IiemB/Croaster/boards/common/src/CroasterDisplayAnimation.cpp

#include "CroasterDisplayAnimation.h"

#include <Adafruit_GFX.h>

namespace {
const uint8_t PROGMEM kFireFrames[28][288] = {
    {0,  0,   12,  0,   0,   0,   0,  0,   14,  0,   0,   0,   0,  0,   15,  128, 0,   0,   0,  0,   9,   192, 0,   0,
     0,  0,   24,  224, 0,   0,   0,  0,   24,  56,  0,   0,   0,  0,   56,  28,  0,   0,   0,  0,   48,  14,  0,   0,
     0,  0,   48,  7,   0,   0,   0,  0,   96,  3,   128, 0,   0,  0,   192, 1,   192, 0,   0,  0,   192, 0,   224, 0,
     0,  1,   128, 0,   48,  0,   0,  3,   128, 0,   56,  0,   0,  7,   0,   0,   28,  0,   0,  6,   0,   192, 12,  0,
     0,  12,  0,   224, 6,   0,   0,  24,  0,   240, 7,   0,   0,  56,  0,   248, 3,   0,   0,  112, 0,   220, 1,   128,
     0,  96,  0,   204, 1,   128, 0,  192, 0,   198, 0,   192, 1,  128, 0,   195, 0,   192, 3,  128, 0,   195, 0,   96,
     3,  0,   0,   193, 128, 96,  3,  0,   192, 193, 128, 96,  6,  0,   224, 192, 128, 48,  6,  1,   240, 128, 192, 48,
     12, 1,   185, 128, 192, 48,  12, 3,   31,  0,   192, 48,  12, 3,   6,   0,   192, 48,  12, 3,   0,   0,   192, 48,
     12, 3,   0,   0,   192, 48,  12, 2,   0,   0,   192, 48,  12, 3,   0,   1,   128, 48,  12, 3,   0,   1,   128, 48,
     12, 3,   128, 3,   128, 96,  6,  1,   128, 3,   0,   96,  6,  0,   224, 6,   0,   224, 7,  0,   96,  6,   0,   192,
     3,  0,   0,   0,   0,   192, 3,  128, 0,   0,   1,   128, 1,  192, 0,   0,   3,   0,   0,  224, 0,   0,   7,   0,
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
    display.clearDisplay();
    display.drawBitmap(xPos, yPos, kFireFrames[frame], FRAME_WIDTH, FRAME_HEIGHT, 1);
    display.display();
    frame = (frame + 1) % FRAME_COUNT;
    delay(FRAME_DELAY);
}

void CroasterDisplayAnimation::reset() {
    frame = 0;
}
