IiemB/Croaster/croaster/src/CroasterCommandHandler.cpp

#include "CroasterCommandHandler.h"

#include <ArduinoJson.h>

#include "CroasterConstants.h"
#include "CroasterWiFiManager.h"
#if defined(ESP32)
#    include <WiFi.h>
#elif defined(ESP8266)
#    include <ESP8266WiFi.h>
#endif

CroasterCommandHandler::CroasterCommandHandler(CroasterCore& core, CroasterDisplay* display, int8_t ledPin,
                                               uint8_t ledOnLevel)
    : croaster(core)
    , display(display)
    , ledPin(ledPin)
    , ledOnLevel(ledOnLevel) {}

void CroasterCommandHandler::onCommand(const String& command, CommandFn fn) {
    customCommands[command] = fn;
}

void CroasterCommandHandler::onJsonCommand(const String& key, CommandFn fn) {
    customJsonCommands[key] = fn;
}

void CroasterCommandHandler::begin() {
    if (ledPin >= 0) {
        pinMode(ledPin, OUTPUT);
        digitalWrite(ledPin, (ledOnLevel == HIGH) ? LOW : HIGH);
    }
}

void CroasterCommandHandler::loop() {
    unsigned long now = millis();

    if (blinking && now - lastBlinkTime >= blinkDelay) {
        ledState = !ledState;
        if (ledPin >= 0)
            digitalWrite(ledPin, ledState ? ledOnLevel : ((ledOnLevel == HIGH) ? LOW : HIGH));
        if (display)
            display->blinkIndicator(ledState);
        lastBlinkTime = now;
        blinkCount++;

        if (blinkCount >= blinkTotal) {
            blinking = false;
            if (ledPin >= 0)
                digitalWrite(ledPin, (ledOnLevel == HIGH) ? LOW : HIGH); // turn off when done
            if (display)
                display->blinkIndicator(false); // turn off when done
        }
    }
}

bool CroasterCommandHandler::handle(const String& json, String& responseOut) {
    JsonDocument doc;

    if (deserializeJson(doc, json)) {
        debugln("# Invalid JSON command : " + json);
        return false;
    }

    responseOut = "";

    if (doc["command"].is<String>()) {
        JsonObject json = doc.as<JsonObject>();

        handleBasicCommand(json, responseOut);

        return true;
    }

    if (doc["command"].is<JsonObject>()) {
        JsonObject obj = doc["command"];

        handleJsonCommand(obj, responseOut);

        return true;
    }

    return false;
}

void CroasterCommandHandler::handleBasicCommand(const JsonObject& json, String& responseOut) {
    if (!json["command"].is<String>())
        return;

    String command = json["command"].as<String>();

    if (command == "getArtisanData") {
        int id = json["id"].as<int>();

        responseOut = croaster.getJsonData(id);
    } else if (command == "restartesp") {
        ESP.restart();
    } else if (command == "erase") {
        CroasterWiFiManager::erase();
    } else if (command == "dummyToggle") {
        croaster.toggleDummyData();
    } else if (command == "rotateScreen") {
        if (display)
            display->rotateScreen();
    } else if (command == "blink") {
        blinkBuiltinLED();
    } else if (command == "displayToggle") {
        if (display)
            display->displayToggle();
    } else if (command == "getDeviceInfo") {
        bool darkMode = (display != nullptr) ? display->isDarkMode() : true;
        int brightness = (display != nullptr) ? display->getBrightness() : 100;
        responseOut = genResponseCommand(command, croaster.getDeviceInfo(darkMode, brightness));
    } else if (command == "getExtra") {
        responseOut = genResponseCommand(command, getExtraData());
    } else {
        // Custom implementation-defined command (registered via onCommand()).
        auto it = customCommands.find(command);
        if (it != customCommands.end()) {
            String resp = it->second(json);
            if (!resp.isEmpty())
                responseOut = resp;
        }
    }
}

void CroasterCommandHandler::handleJsonCommand(const JsonObject& json, String& responseOut) {
    if (json["tempUnit"].is<String>()) {
        String tempUnit = json["tempUnit"].as<String>();

        croaster.changeTemperatureUnit(tempUnit);
    }

    if (json["interval"].is<int>()) {
        int interval = json["interval"].as<int>();

        if (interval >= 1)
            croaster.changeIntervalSendData(interval);
    }

    if (json["correctionBt"].is<double>()) {
        double correctionBt = json["correctionBt"].as<double>();

        croaster.changeCorrectionBt(correctionBt);
    }

    if (json["correctionEt"].is<double>()) {
        double correctionEt = json["correctionEt"].as<double>();

        croaster.changeCorrectionEt(correctionEt);
    }

    if (json["wifiConnect"].is<JsonObject>()) {
        JsonObject obj = json["wifiConnect"];

        if (obj["ssid"].is<String>() && obj["pass"].is<String>()) {
            String ssid = obj["ssid"].as<String>();
            String pass = obj["pass"].as<String>();

            WiFi.begin(ssid.c_str(), pass.c_str());

            debugln("# Connecting to " + ssid);
        }
    }

    // Custom implementation-defined nested JSON commands (registered via onJsonCommand()).
    for (auto& entry : customJsonCommands) {
        if (json[entry.first].is<JsonVariant>()) {
            String resp = entry.second(json);
            if (!resp.isEmpty())
                responseOut = resp;
        }
    }
}

void CroasterCommandHandler::blinkBuiltinLED(uint8_t times, unsigned long blinkDelay) {
    blinkTotal = times * 2; // on/off = 2 toggles per blink
    blinkCount = 0;
    lastBlinkTime = millis();
    blinkDelay = blinkDelay;
    ledState = false;

    blinking = true;
}

String CroasterCommandHandler::genResponseCommand(const String command, const String response) {
    JsonDocument doc;

    JsonDocument responseDoc;

    doc["command"] = command;

    if (!response.isEmpty() && !deserializeJson(responseDoc, response)) {
        doc["response"] = responseDoc;
    }

    String jsonOutput;

    serializeJson(doc, jsonOutput);

    return jsonOutput;
}

String CroasterCommandHandler::genRandomString(int length) {
    const char charset[] = "0123456789"
                           "ABCDEFGHIJKLMNOPQRSTUVWXYZ"
                           "abcdefghijklmnopqrstuvwxyz";

    String result;

    for (int i = 0; i < length; i++) {
        result += charset[random(0, sizeof(charset) - 1)];
    }

    return result;
}

String CroasterCommandHandler::getExtraData() {
    /*
   NOTE
   You can add more fields to the JSON document that will be readed by ICRM app,
   such as historical data or other sensor readings.
   */

    JsonDocument doc;

    doc["string"] = genRandomString(10);
    doc["number"] = random(100, 999);
    doc["boolean"] = random(0, 2) == 1;

    String jsonOutput;

    serializeJson(doc, jsonOutput);

    return jsonOutput;
}
