IiemB/Croaster/boards/common/src/CroasterDisplaySSD1306.cpp

#include "CroasterDisplaySSD1306.h"

#include <CroasterConstants.h>
#include <CroasterDeviceIdentity.h>
#include <Wire.h>

#include "CroasterDisplayAnimation.h"

CroasterDisplaySSD1306::CroasterDisplaySSD1306(CroasterCore& croaster, uint8_t i2cAddr)
    : CroasterDisplay(croaster)
    , display(SCREEN_WIDTH, SCREEN_HEIGHT, &Wire, OLED_RESET)
    , i2cAddress(i2cAddr) {}

void CroasterDisplaySSD1306::begin() {
    hasDisplay = isOledPresent();

    if (!hasDisplay) {
        debugln(F("# No display found"));
        return;
    }

    if (!display.begin(SSD1306_SWITCHCAPVCC, i2cAddress)) {
        debugln(F("# SSD1306 allocation failed"));
        return;
    }

    display.clearDisplay();
    display.setTextColor(SSD1306_WHITE);
    debugln(F("# SSD1306 initialization succeed"));
    splash();

    display.setTextWrap(false);
}

void CroasterDisplaySSD1306::drawHeader() {
    if (!hasDisplay)
        return;

    String text = "CROASTER V" + String(version);

    if (isIpShowed && !ipAddr.isEmpty()) {
        text = ipAddr;
    }

    display.setTextSize(1);
    display.setCursor(0, 0);
    display.print(text);
}

void CroasterDisplaySSD1306::drawTemperature(String label, double temp, double ror, int yCursor) {
    if (!hasDisplay)
        return;

    String tempText = isnan(temp) ? "N/A" : String(temp, 1) + tempUnit;
    int tempX = display.width() - (18 * tempText.length()) + 3;

    display.setTextSize(1);
    display.setCursor(0, yCursor);
    display.print(label);

    display.setTextSize(3);
    display.setCursor(tempX, yCursor);
    display.print(tempText);

    if (!isnan(temp)) {
        String rorText = String((int)round(ror));

        if (ror >= 0 && ror < 10)
            rorText = String((double)ror, 1);

        display.setTextSize(1);
        display.setCursor(0, yCursor + 14);
        display.print(rorText);
    }
}

void CroasterDisplaySSD1306::splash() {
    if (!hasDisplay)
        return;

    display.clearDisplay();
    CroasterDisplayAnimation animation;

    for (int16_t i = 0; i < 50; i += 1) {
        animation.showFire(display);
        delay(1);
    }
}

bool CroasterDisplaySSD1306::isOledPresent() {
    Wire.begin();
    delay(100);

    Wire.beginTransmission(i2cAddress);
    return Wire.endTransmission() == 0;
}

void CroasterDisplaySSD1306::loop() {
    if (!hasDisplay)
        return;

    unsigned long now = millis();

    // === Invert screen ===
    if (now - lastInversionToggle >= (isDisplayInverted ? inversionDuration : inversionInterval)) {
        isDisplayInverted = !isDisplayInverted;
        lastInversionToggle = now;
        display.invertDisplay(isDisplayInverted);
        debugln(isDisplayInverted ? "# Display Inverted to Prevent Burn-In" : "# Display Reverted to Normal");
    }

    if (isUpdatingFirmware) {
        if (!isDisplayOn)
            displayToggle();

        return;
    }

    // === Update screen ===
    if (now - lastUpdate >= 1000) {
        lastUpdate = now;

        et = _core->tempEt;
        rorEt = _core->rorEt;
        bt = _core->tempBt;
        rorBt = _core->rorBt;
        tempUnit = _core->temperatureUnit();
        ipAddr = CroasterDeviceIdentity::ipAddress();

        display.clearDisplay();
        drawHeader();

        drawTemperature("BT", bt, rorBt, 16);
        drawTemperature("ET", et, rorEt, 43);

        display.display();
    }

    // === Show ip address ===
    if (now - lastShowIpToggle >= (isIpShowed ? 5000 : 10000)) {
        isIpShowed = !isIpShowed;
        lastShowIpToggle = now;
    }
}

void CroasterDisplaySSD1306::rotateScreen() {
    if (!hasDisplay)
        return;

    if (screenRotation > 0)
        screenRotation = 0;
    else
        screenRotation = 2;

    display.setRotation(screenRotation);
    display.display();
}

void CroasterDisplaySSD1306::blinkIndicator(bool state) {
    if (!hasDisplay)
        return;

    display.fillCircle(124, 3, 3, state ? 1 : 0);
    display.display();
}

void CroasterDisplaySSD1306::displayToggle() {
    if (!hasDisplay)
        return;

    isDisplayOn = !isDisplayOn;

    display.ssd1306_command(isDisplayOn ? SSD1306_DISPLAYON : SSD1306_DISPLAYOFF);
}

void CroasterDisplaySSD1306::updateFirmwareUpdateProgress(int progress) {
    if (!hasDisplay)
        return;

    String progressText = String(progress);
    while (progressText.length() < 3)
        progressText = "_" + progressText;
    progressText += " %";

    int lineLength = (progress * 128) / 100;

    display.clearDisplay();
    display.setTextColor(WHITE);
    display.setTextSize(1);
    display.setFont(NULL);
    display.setCursor(0, 15);
    display.setTextWrap(0);
    display.setCursor(13, 15);
    display.println("Updating Firmware");
    display.setCursor(0, 30);
    display.setTextWrap(0);
    display.setCursor(49, 30);
    display.println(progressText);
    display.drawLine(0, 50, lineLength, 50, 1);
    display.display();
}

void CroasterDisplaySSD1306::updatingStatusToggle(bool isUpdating) {
    if (isUpdatingFirmware == isUpdating)
        return;

    isUpdatingFirmware = isUpdating;
}

bool CroasterDisplaySSD1306::isFirmwareUpdating() const {
    return isUpdatingFirmware;
}
