IiemB/Croaster/croaster/src/CroasterCommandHandler.h

#pragma once
#include <Arduino.h>
#include <ArduinoJson.h>

#include <functional>
#include <map>

#include "CroasterConstants.h"
#include "CroasterCore.h"
#include "CroasterDisplay.h"

/**
 * @class CroasterCommandHandler
 * @brief Handles incoming commands and manages device behavior accordingly.
 */
class CroasterCommandHandler {
public:
    /// Signature for custom command callbacks.
    using CommandFn = std::function<String(const JsonObject& json)>;

private:
    CroasterCore& croaster;
    CroasterDisplay* display; ///< Optional display (may be nullptr).

    bool blinking = false;
    uint8_t blinkCount = 0;
    uint8_t blinkTotal = 0;
    unsigned long lastBlinkTime = 0;
    unsigned long blinkDelay = 250;
    bool ledState = false;

    int8_t ledPin;      ///< Built-in LED pin (-1 = no LED).
    uint8_t ledOnLevel; ///< Active level for the LED (LOW or HIGH).

    std::map<String, CommandFn> customCommands;     ///< Custom basic commands.
    std::map<String, CommandFn> customJsonCommands; ///< Custom nested JSON commands.

    /**
     * @brief Handles basic commands such as restart or erase.
     * @param json The JSON object containing the command.
     * @param responseOut The response to send back.
     */
    void handleBasicCommand(const JsonObject& json, String& responseOut);

    /**
     * @brief Handles JSON-formatted commands.
     * @param json The JSON object containing the command.
     * @param responseOut The response to send back.
     */
    void handleJsonCommand(const JsonObject& json, String& responseOut);

    /**
     * @brief Blinks the built-in LED a specified number of times.
     * @param times The number of times to blink.
     * @param blinkDelay The delay between blinks in milliseconds.
     */
    void blinkBuiltinLED(uint8_t times = 2, unsigned long blinkDelay = 250);

    /**
     * @brief Generates a random string of a specified length.
     * @param length The length of the random string to generate.
     * @return A random string of the specified length.
     */
    String genRandomString(int length);

    /**
     * @brief Retrieves extra data for the "extra" command.
     * @return A JSON-formatted string containing extra data.
     */
    String getExtraData();

public:
    /**
     * @brief Constructs a CroasterCommandHandler instance.
     * @param core Reference to the CroasterCore instance.
     * @param display Optional display for the LED blink indicator (may be nullptr).
     * @param ledPin Built-in LED pin (defaults to LED_BUILTIN; pass -1 to disable).
     * @param ledOnLevel Active level for the LED (LOW = active-low, HIGH = active-high).
     */
    CroasterCommandHandler(CroasterCore& core, CroasterDisplay* display = nullptr, int8_t ledPin = LED_BUILTIN,
                           uint8_t ledOnLevel = LOW);

    /**
     * @brief Initializes the CroasterCommandHandler.
     */
    void begin();

    /**
     * @brief Handles tasks related to command processing in the main loop.
     */
    void loop();

    /**
     * @brief Processes an incoming command.
     * @param json The command in JSON format.
     * @param responseOut The response to send back.
     * @return True if the command was handled successfully, false otherwise.
     */
    bool handle(const String& json, String& responseOut);

    /**
     * @brief Registers a custom basic (string) command without modifying the
     *        library core. Example: {"command":"ping"}.
     * @param command The command string.
     * @param fn Callback invoked when the command arrives; returns a response
     *           string (empty = no response sent).
     */
    void onCommand(const String& command, CommandFn fn);

    /**
     * @brief Registers a custom nested JSON command key without modifying the
     *        library core. Example: {"command":{"myKey":...}}.
     * @param key The JSON key inside the "command" object.
     * @param fn Callback invoked when the key is present; receives the nested
     *           "command" object and returns a response string (empty = none).
     */
    void onJsonCommand(const String& key, CommandFn fn);

    /**
     * @brief Generates a JSON response for a given command (usable by custom
     *        command callbacks).
     * @param command The command for which to generate the response.
     * @param response The response message to include in the JSON.
     * @return A JSON-formatted string containing the command and response.
     */
    String genResponseCommand(const String command, const String response);
};
