IiemB/Croaster/boards/common/src/CroasterDisplayAnimation.h

#pragma once

#include <Adafruit_SSD1306.h>
#include <Arduino.h>

/**
 * @class CroasterDisplayAnimation
 * @brief Fire animation used on the splash screen (reference SSD1306 display).
 */
class CroasterDisplayAnimation {
public:
    CroasterDisplayAnimation(int16_t x = 40, int16_t y = 8);

    void showFire(Adafruit_SSD1306& display);
    void reset();

private:
    static constexpr uint16_t FRAME_DELAY = 42;
    static constexpr uint8_t FRAME_WIDTH = 48;
    static constexpr uint8_t FRAME_HEIGHT = 48;
    static constexpr uint8_t FRAME_COUNT = 28;

    uint8_t frame = 0;
    int16_t xPos;
    int16_t yPos;
};
