IiemB/Croaster/croaster/src/CroasterOtaHandler.h

#pragma once

#include <Arduino.h>

#include "CroasterConstants.h"
#include "CroasterWiFiManager.h"
#if defined(ESP32)
#    include <Update.h>
#elif defined(ESP8266)
#    include <Updater.h>
#endif

/**
 * @class CroasterOtaHandler
 * @brief Handles Over-The-Air (OTA) firmware updates via WebSocket and BLE.
 */
class CroasterOtaHandler {
public:
    /**
     * @brief Constructor for CroasterOtaHandler.
     */
    CroasterOtaHandler();

    /**
     * @brief Initializes the OTA process with the total size of the update.
     * @param totalSize The total size of the OTA update in bytes.
     */
    void begin(uint32_t totalSize);

    /**
     * @brief Processes incoming binary data for the OTA update.
     * @param data Pointer to the binary data.
     * @param len Length of the binary data.
     * @return A JSON string indicating the status of the OTA process and progress information.
     */
    String handleBinary(uint8_t* data, size_t len);

    /**
     * @brief Checks if the OTA process is currently receiving data.
     * @return True if data is being received, false otherwise.
     */
    bool isReceiving() const;

    /**
     * @brief Checks if the OTA process is complete.
     */
    void handleState();

    /**
     * @brief Gets the total size of the OTA update.
     * @return The total size in bytes.
     */
    uint32_t getTotal() const;

    /**
     * @brief Gets the number of bytes written so far during the OTA process.
     * @return The number of bytes written.
     */
    uint32_t getWritten() const;

private:
    /**
     * @enum State
     * @brief Represents the current state of the OTA process.
     */
    enum class State {
        Idle,      ///< No OTA process is active.
        Receiving, ///< OTA packets are being received.
        Failed,    ///< An error occurred during the OTA process.
        Done       ///< OTA process is complete.
    };

    State state = State::Idle; ///< Current state of the OTA process.
    uint32_t totalSize = 0;    ///< Total size of the OTA update in bytes.
    uint32_t written = 0;      ///< Number of bytes written so far.

    /**
     * @brief Resets the internal state of the handler to its initial values.
     */
    void resetState();

    /**
     * @brief Finalizes the OTA process.
     * @param hasError If true, aborts the update and restarts. If false, ends successfully and restarts.
     */
    void finalize(bool hasError = false);
};
